kadarkarai474/eSim_PCB_Design_Project_Files/3DMODELS/629105150521_20_28rev1_29.stp

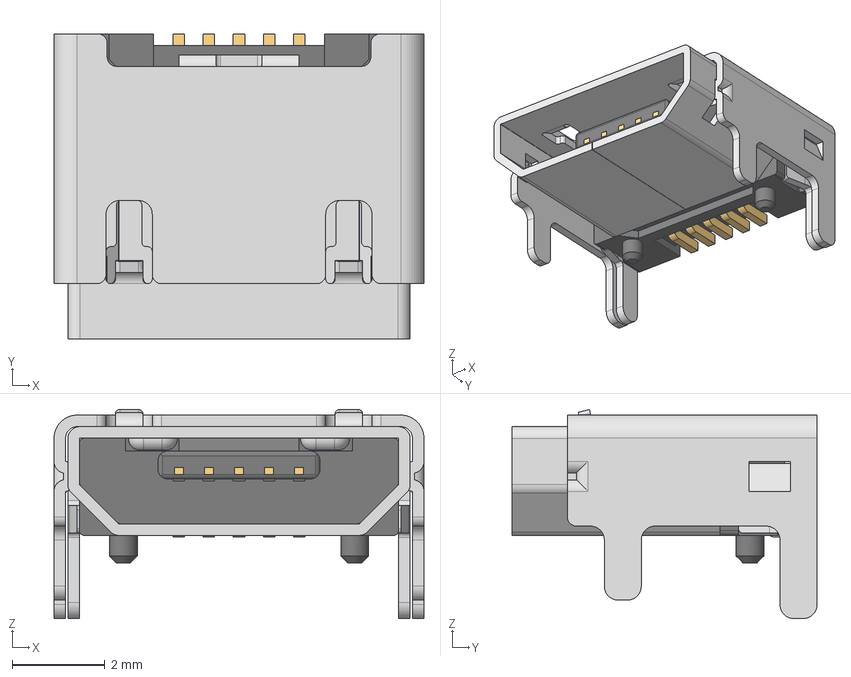
[picture p29: CAD file, 2026-08-23]
3DMODELS/629105150521_20_28rev1_29.stp
8.00 x 6.60 x 4.52 mm
629105150521_Housing
629105150521_Pin1 x 4
629105150521_Pin2
629105150521_Shielding2
629105150521_Shielding
